amead77/SCAD-13-inch-rack/330mm rack feet.scad

include <330mm rack defines.scad>;

module footer() {
    


}
