amead77/SCAD-13-inch-rack/330mm rack tray.scad

include <330mm rack defines.scad>;
include <330mm rack posts.scad>;


/*
// next 2 lines used only by my 'on save' script. can be ignored otherwise.
// AUTO-V
version = "v0.1-2026/05/05r12";
*/


// blank_1U_front_panel(holes)
// Public — generates a 1U blanking front panel with rounded or square edges.
// holes: mounting holes per side (2, 3, 4, or 6). Default: front_panel_hole_count.
// e.g. blank_1U_front_panel(holes=2);
module blank_1U_front_panel(holes = front_panel_hole_count) {
    difference() {
        union() {
            if (front_panel_edge_radius > 0) {
                translate([front_panel_undersizing + front_panel_edge_radius, 0, front_panel_undersizing + front_panel_edge_radius]) {
                    minkowski() {
                        cube([rack_width - (front_panel_undersizing*2) - (front_panel_edge_radius*2), front_panel_thickness, u_height - (front_panel_undersizing*2) - (front_panel_edge_radius*2)]);
                        rotate([90,0,0]) {
                            cylinder(r=front_panel_edge_radius, h=0.01, center=true, $fn=32);
                        }
                    }
                }
            } else {
                translate([front_panel_undersizing, 0, front_panel_undersizing]) {
                    cube([rack_width - (front_panel_undersizing*2), front_panel_thickness, u_height - (front_panel_undersizing*2)]);
                }
            }
        }
        
        translate([0, -1, 0]){
            holes(holes);
            translate([rack_width - post_width, 0, 0]) {
                holes(holes);
            }
        }
    }
}


// front_panel_hole_at(x_pos, z_pos)
// Internal helper — subtracts a single M6 screw hole through the front panel at the given X and Z position.
module front_panel_hole_at(x_pos, z_pos) {
    translate([x_pos, post_width/2, z_pos]) {
        rotate([90,0,0]) {
            cylinder(d=hole_d, h=post_width, center=true, $fn=32);
        }
    }
}


// front_panel_2U_holes(holes)
// Internal helper — subtracts the correct pattern of screw holes for a 2U front panel.
// holes: 2 = one per side per U (4 total per side), 6 = three per side per U, default = 4.
module front_panel_2U_holes(holes = 4) {
    if (holes == 2) {
        front_panel_hole_at(post_width/2, hole_offset_z/2);
        front_panel_hole_at(post_width/2, u_height + (hole_offset_z/2) + (hole_spacing * 2));
        front_panel_hole_at(rack_width - post_width/2, hole_offset_z/2);
        front_panel_hole_at(rack_width - post_width/2, u_height + (hole_offset_z/2) + (hole_spacing * 2));
    } else if (holes == 6) {
        front_panel_hole_at(post_width/2, hole_offset_z/2);
        front_panel_hole_at(post_width/2, hole_offset_z/2 + hole_spacing);
        front_panel_hole_at(post_width/2, hole_offset_z/2 + (hole_spacing * 2));
        front_panel_hole_at(post_width/2, u_height + hole_offset_z/2);
        front_panel_hole_at(post_width/2, u_height + hole_offset_z/2 + hole_spacing);
        front_panel_hole_at(post_width/2, u_height + hole_offset_z/2 + (hole_spacing * 2));

        front_panel_hole_at(rack_width - post_width/2, hole_offset_z/2);
        front_panel_hole_at(rack_width - post_width/2, hole_offset_z/2 + hole_spacing);
        front_panel_hole_at(rack_width - post_width/2, hole_offset_z/2 + (hole_spacing * 2));
        front_panel_hole_at(rack_width - post_width/2, u_height + hole_offset_z/2);
        front_panel_hole_at(rack_width - post_width/2, u_height + hole_offset_z/2 + hole_spacing);
        front_panel_hole_at(rack_width - post_width/2, u_height + hole_offset_z/2 + (hole_spacing * 2));
    } else {
        // Default 2U pattern: 4 holes per side using the 2-hole 1U pattern repeated across both U sections.
        front_panel_hole_at(post_width/2, hole_offset_z/2);
        front_panel_hole_at(post_width/2, hole_offset_z/2 + (hole_spacing * 2));
        front_panel_hole_at(post_width/2, u_height + hole_offset_z/2);
        front_panel_hole_at(post_width/2, u_height + hole_offset_z/2 + (hole_spacing * 2));

        front_panel_hole_at(rack_width - post_width/2, hole_offset_z/2);
        front_panel_hole_at(rack_width - post_width/2, hole_offset_z/2 + (hole_spacing * 2));
        front_panel_hole_at(rack_width - post_width/2, u_height + hole_offset_z/2);
        front_panel_hole_at(rack_width - post_width/2, u_height + hole_offset_z/2 + (hole_spacing * 2));
    }
}


// blank_2U_front_panel(holes)
// Public — generates a 2U blanking front panel.
// holes: mounting holes per side (2, 4, or 6). Default: 4.
// e.g. blank_2U_front_panel(holes=4);
module blank_2U_front_panel(holes = 4) {
    difference() {
        union() {
            if (front_panel_edge_radius > 0) {
                translate([front_panel_undersizing + front_panel_edge_radius, 0, front_panel_undersizing + front_panel_edge_radius]) {
                    minkowski() {
                        cube([rack_width - (front_panel_undersizing*2) - (front_panel_edge_radius*2), front_panel_thickness, (u_height * 2) - (front_panel_undersizing*2) - (front_panel_edge_radius*2)]);
                        rotate([90,0,0]) {
                            cylinder(r=front_panel_edge_radius, h=0.01, center=true, $fn=32);
                        }
                    }
                }
            } else {
                translate([front_panel_undersizing, 0, front_panel_undersizing]) {
                    cube([rack_width - (front_panel_undersizing*2), front_panel_thickness, (u_height * 2) - (front_panel_undersizing*2)]);
                }
            }
        }

        translate([0, -1, 0]) {
            front_panel_2U_holes(holes);
        }
    }
}


// blank_05U_front_panel()
// Public — generates a 0.5U blanking front panel (used at top and bottom of the rack assembly).
// No parameters; all sizing comes from defines.
// e.g. blank_05U_front_panel();
module blank_05U_front_panel() {
    // 0.5U panel: height = hole_offset_z (12.7mm), one hole per side centred at hole_offset_z/2
    half_u = hole_offset_z * 2;
    difference() {
        union() {
            if (front_panel_edge_radius > 0) {
                translate([front_panel_undersizing + front_panel_edge_radius, 0, front_panel_undersizing + front_panel_edge_radius]) {
                    minkowski() {
                        cube([rack_width - (front_panel_undersizing*2) - (front_panel_edge_radius*2), front_panel_thickness, half_u - (front_panel_undersizing*2) - (front_panel_edge_radius*2)]);
                        rotate([90,0,0]) {
                            cylinder(r=front_panel_edge_radius, h=0.01, center=true, $fn=32);
                        }
                    }
                }
            } else {
                translate([front_panel_undersizing, 0, front_panel_undersizing]) {
                    cube([rack_width - (front_panel_undersizing*2), front_panel_thickness, half_u - (front_panel_undersizing*2)]);
                }
            }
        }

        // 2 holes per side, centred vertically in the 0.5U panel
        translate([0, -1, 0]) {
            translate([post_width/2, post_width/2, hole_offset_z/2]) {
                rotate([90,0,0]) {
                    cylinder(d=hole_d, h=post_width, center=true, $fn=32);
                }
            }
            translate([post_width/2, post_width/2, hole_offset_z*3/2]) {
                rotate([90,0,0]) {
                    cylinder(d=hole_d, h=post_width, center=true, $fn=32);
                }
            }


            translate([rack_width - post_width/2, post_width/2, hole_offset_z/2]) {
                rotate([90,0,0]) {
                    cylinder(d=hole_d, h=post_width, center=true, $fn=32);
                }
            }
            translate([rack_width - post_width/2, post_width/2, hole_offset_z*3/2]) {
                rotate([90,0,0]) {
                    cylinder(d=hole_d, h=post_width, center=true, $fn=32);
                }
            }
        }
    }
}


// post_base_join_panel(doublewide, thickness)
// Public — compact panel to join one post footprint (or two for doublewide) to a base joiner using 2 holes per post.
// doublewide: 0=single post width, 1=double post width. thickness: panel thickness in mm.
// e.g. post_base_join_panel();
// e.g. post_base_join_panel(doublewide=1, thickness=4);
module post_base_join_panel(doublewide = 0, thickness = front_panel_thickness) {
    panel_width = (doublewide == 1) ? (post_width * 2) : post_width;
    panel_height = hole_offset_z * 2;

    difference() {
        cube([panel_width, thickness, panel_height]);

        // Two-hole pattern per post footprint, matching the 0.5U vertical spacing.
        for (x_pos = (doublewide == 1) ? [post_width/2, post_width + post_width/2] : [post_width/2]) {
            translate([x_pos, thickness/2, hole_offset_z/2]) {
                rotate([90,0,0]) {
                    cylinder(d=hole_d, h=thickness + 2, center=true, $fn=32);
                }
            }
            translate([x_pos, thickness/2, hole_offset_z*3/2]) {
                rotate([90,0,0]) {
                    cylinder(d=hole_d, h=thickness + 2, center=true, $fn=32);
                }
            }
        }
    }
}

// side_slide(count, side)
// Internal helper — builds the 1U tray side wall and slide tabs that engage the post slot.
// count: number of slide tabs (1–3, matching post hole count per U). side: 0=left, 1=right.
module side_slide(count = 3, side = 0) {
    union() {
        if (side == 0) {
            translate([post_width+post_slide_width+tray_post_clearance, front_panel_thickness, 0]) {
                if (count == 1) {
                    cube([tray_side_thickness, rack_width, u_height - hole_spacing * 2]);
                } else if (count == 2) {
                    cube([tray_side_thickness, rack_width, u_height - hole_spacing]);
                } else if (count >= 3) {
                cube([tray_side_thickness, rack_width, u_height-1]);
                }
            }
            if (count >= 1) {
                translate([post_width+tray_post_clearance, front_panel_thickness, (hole_offset_z/2)-(post_slide_cutout/2.1)]) {
                    cube([post_slide_width, rack_width, post_slide_cutout-hole_clearance]);
                }
            }
            if (count >= 2) {
                translate([post_width+tray_post_clearance, front_panel_thickness, (hole_offset_z/2)-(post_slide_cutout/2.1)+ hole_spacing]) {
                    cube([post_slide_width, rack_width, post_slide_cutout-hole_clearance]);
                }
            }
            if (count >= 3) {
                translate([post_width+tray_post_clearance, front_panel_thickness, (hole_offset_z/2)-(post_slide_cutout/2.1)+ hole_spacing * 2]) {
                    cube([post_slide_width, rack_width, post_slide_cutout-hole_clearance]);
                }
            }
        } else {
            translate([rack_width - post_width - post_slide_width - tray_post_clearance - tray_side_thickness, front_panel_thickness, 0]) {
                if (count == 1) {
                    cube([tray_side_thickness, rack_width, u_height - hole_spacing * 2]);
                } else if (count == 2) {
                    cube([tray_side_thickness, rack_width, u_height - hole_spacing]);
                } else if (count >= 3) {
                    cube([tray_side_thickness, rack_width, u_height-1]);
                }
            }
            if (count >= 1) {
                translate([rack_width - post_width - tray_post_clearance - post_slide_width, front_panel_thickness, (hole_offset_z/2)-(post_slide_cutout/2.1)]) {
                    cube([post_slide_width, rack_width, post_slide_cutout-hole_clearance]);
                }
            }
            if (count >= 2) {
                translate([rack_width - post_width - tray_post_clearance - post_slide_width, front_panel_thickness, (hole_offset_z/2)-(post_slide_cutout/2.1)+ hole_spacing]) {
                    cube([post_slide_width, rack_width, post_slide_cutout-hole_clearance]);
                }
            }
            if (count >= 3) {
                translate([rack_width - post_width - tray_post_clearance - post_slide_width, front_panel_thickness, (hole_offset_z/2)-(post_slide_cutout/2.1)+ hole_spacing * 2]) {
                    cube([post_slide_width, rack_width, post_slide_cutout-hole_clearance]);
                }
            }
        }
    }
}


// tray_side_height_2U(count)
// Internal helper — generates the side wall body for a 2U tray at the correct height for the given tab count.
// count: 1–6, controls wall height to match the slide tab positions.
module tray_side_height_2U(count = 3) {
    if (count <= 1) {
        cube([tray_side_thickness, rack_width, u_height - hole_spacing * 2]);
    } else if (count == 2) {
        cube([tray_side_thickness, rack_width, u_height - hole_spacing]);
    } else if (count == 3) {
        cube([tray_side_thickness, rack_width, u_height - 1]);
    } else if (count == 4) {
        cube([tray_side_thickness, rack_width, u_height + (u_height - hole_spacing * 2)]);
    } else if (count == 5) {
        cube([tray_side_thickness, rack_width, u_height + (u_height - hole_spacing)]);
    } else {
        cube([tray_side_thickness, rack_width, (u_height * 2) - 1]);
    }
}


// side_slide_2U(count, side)
// Internal helper — builds the 2U tray side wall and slide tabs that engage the post slot.
// count: number of slide tabs (1–6). side: 0=left, 1=right.
module side_slide_2U(count = 3, side = 0) {
    union() {
        if (side == 0) {
            translate([post_width+post_slide_width+tray_post_clearance, front_panel_thickness, 0]) {
                tray_side_height_2U(count);
            }
            if (count >= 1) {
                translate([post_width+tray_post_clearance, front_panel_thickness, (hole_offset_z/2)-(post_slide_cutout/2.1)]) {
                    cube([post_slide_width, rack_width, post_slide_cutout-hole_clearance]);
                }
            }
            if (count >= 2) {
                translate([post_width+tray_post_clearance, front_panel_thickness, (hole_offset_z/2)-(post_slide_cutout/2.1)+ hole_spacing]) {
                    cube([post_slide_width, rack_width, post_slide_cutout-hole_clearance]);
                }
            }
            if (count >= 3) {
                translate([post_width+tray_post_clearance, front_panel_thickness, (hole_offset_z/2)-(post_slide_cutout/2.1)+ hole_spacing * 2]) {
                    cube([post_slide_width, rack_width, post_slide_cutout-hole_clearance]);
                }
            }
            if (count >= 4) {
                translate([post_width+tray_post_clearance, front_panel_thickness, u_height + (hole_offset_z/2)-(post_slide_cutout/2.1)]) {
                    cube([post_slide_width, rack_width, post_slide_cutout-hole_clearance]);
                }
            }
            if (count >= 5) {
                translate([post_width+tray_post_clearance, front_panel_thickness, u_height + (hole_offset_z/2)-(post_slide_cutout/2.1)+ hole_spacing]) {
                    cube([post_slide_width, rack_width, post_slide_cutout-hole_clearance]);
                }
            }
            if (count >= 6) {
                translate([post_width+tray_post_clearance, front_panel_thickness, u_height + (hole_offset_z/2)-(post_slide_cutout/2.1)+ hole_spacing * 2]) {
                    cube([post_slide_width, rack_width, post_slide_cutout-hole_clearance]);
                }
            }
        } else {
            translate([rack_width - post_width - post_slide_width - tray_post_clearance - tray_side_thickness, front_panel_thickness, 0]) {
                tray_side_height_2U(count);
            }
            if (count >= 1) {
                translate([rack_width - post_width - tray_post_clearance - post_slide_width, front_panel_thickness, (hole_offset_z/2)-(post_slide_cutout/2.1)]) {
                    cube([post_slide_width, rack_width, post_slide_cutout-hole_clearance]);
                }
            }
            if (count >= 2) {
                translate([rack_width - post_width - tray_post_clearance - post_slide_width, front_panel_thickness, (hole_offset_z/2)-(post_slide_cutout/2.1)+ hole_spacing]) {
                    cube([post_slide_width, rack_width, post_slide_cutout-hole_clearance]);
                }
            }
            if (count >= 3) {
                translate([rack_width - post_width - tray_post_clearance - post_slide_width, front_panel_thickness, (hole_offset_z/2)-(post_slide_cutout/2.1)+ hole_spacing * 2]) {
                    cube([post_slide_width, rack_width, post_slide_cutout-hole_clearance]);
                }
            }
            if (count >= 4) {
                translate([rack_width - post_width - tray_post_clearance - post_slide_width, front_panel_thickness, u_height + (hole_offset_z/2)-(post_slide_cutout/2.1)]) {
                    cube([post_slide_width, rack_width, post_slide_cutout-hole_clearance]);
                }
            }
            if (count >= 5) {
                translate([rack_width - post_width - tray_post_clearance - post_slide_width, front_panel_thickness, u_height + (hole_offset_z/2)-(post_slide_cutout/2.1)+ hole_spacing]) {
                    cube([post_slide_width, rack_width, post_slide_cutout-hole_clearance]);
                }
            }
            if (count >= 6) {
                translate([rack_width - post_width - tray_post_clearance - post_slide_width, front_panel_thickness, u_height + (hole_offset_z/2)-(post_slide_cutout/2.1)+ hole_spacing * 2]) {
                    cube([post_slide_width, rack_width, post_slide_cutout-hole_clearance]);
                }
            }
        }
    }
}



// blank_1U_tray(side_count, edge_radius, holes)
// Public — generates a 1U tray with front panel and side slides. Use as a base for custom 1U trays.
// side_count: slide tabs per side (1–3). edge_radius: front panel corner rounding. holes: mounting holes per side.
// e.g. blank_1U_tray(side_count=3, edge_radius=2, holes=2);
module blank_1U_tray(side_count = 3, edge_radius = 2, holes = front_panel_hole_count) {
    //use this as a primitive to make trays.
    blank_1U_front_panel(holes);
    translate([post_width+tray_post_clearance+post_slide_width, 0, front_panel_undersizing]) {
        cube([((rack_width - (post_width*2)) - (tray_post_clearance*2)-(post_slide_width*2)), rack_width+front_panel_thickness, tray_thickness]);
    }
    side_slide(side = 0, count = side_count);
    side_slide(side = 1, count = side_count);
}


// blank_2U_tray(side_count, edge_radius, holes)
// Public — generates a 2U tray with front panel and side slides. Use as a base for custom 2U trays.
// side_count: slide tabs per side (1–6). edge_radius: front panel corner rounding. holes: mounting holes per side.
// e.g. blank_2U_tray(side_count=3, edge_radius=2, holes=4);
module blank_2U_tray(side_count = 3, edge_radius = 2, holes = 4) {
    blank_2U_front_panel(holes);
    translate([post_width+tray_post_clearance+post_slide_width, 0, front_panel_undersizing]) {
        cube([((rack_width - (post_width*2)) - (tray_post_clearance*2)-(post_slide_width*2)), rack_width+front_panel_thickness, tray_thickness]);
    }
    side_slide_2U(side = 0, count = side_count);
    side_slide_2U(side = 1, count = side_count);
}
